open-flight/open-gps/case/concepts/renders/b_stone_cart_side.png

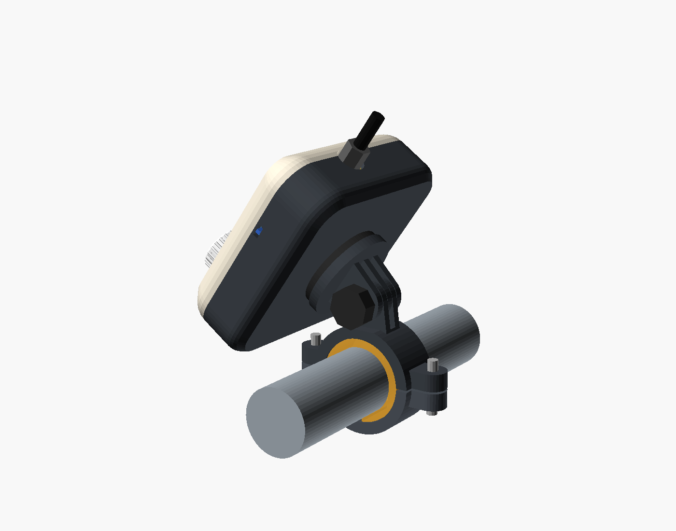
case/concepts/renders/b_stone_cart_side.png
