open-flight/open-gps/case/render_closed.png

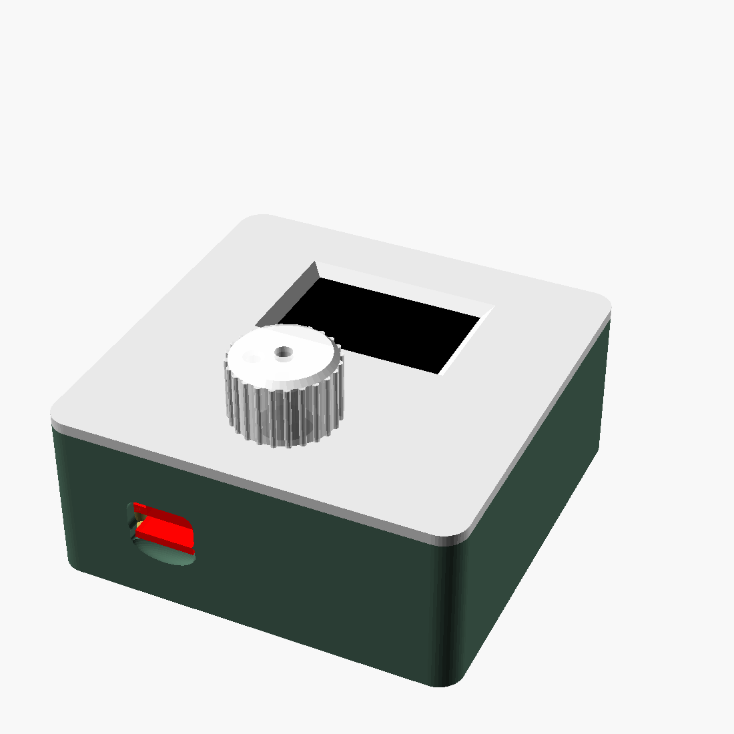
case/render_closed.png
